relikd/cad-mouse-mk2-case-variations/spring/attempts/batch-1/v3.png

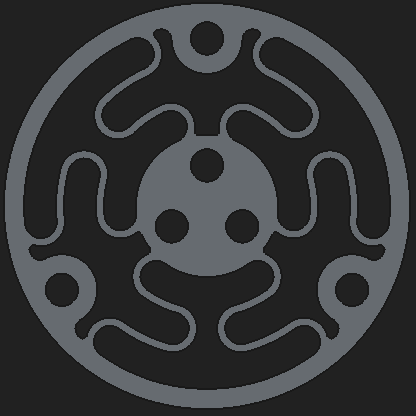
spring/attempts/batch-1/v3.png
