relikd/cad-mouse-mk2-case-variations/spring/attempts/batch-1/v17-winner.png

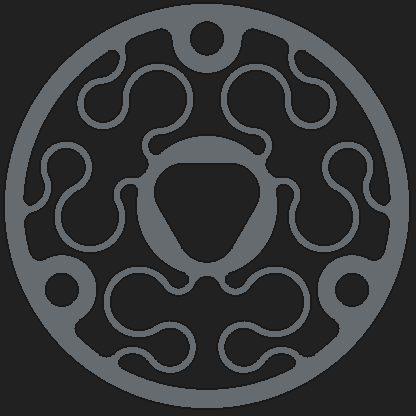
spring/attempts/batch-1/v17-winner.png
