relikd/cad-mouse-mk2-case-variations/_pcb/nikki-mcu.FCStd

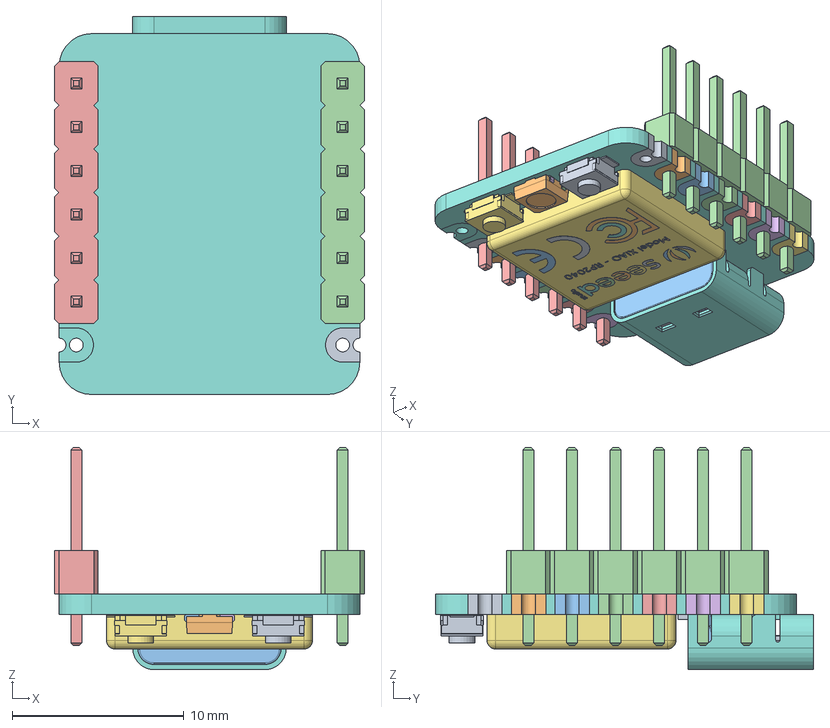
[picture p36: CAD file, 2026-06-23]
_pcb/nikki-mcu.FCStd
18.0 x 22.0 x 12.9 mm
type-c v2
type-c v001
type-c v002
type-c v003
type-c v004
type-c v005
type-c v006
type-c v007
type-c v008
type-c v009
type-c v010
type-c v011
type-c v012
type-c v013
type-c v014
type-c v015
type-c v016
type-c v017
type-c v018
type-c v019
type-c v020
type-c v021
type-c v022
type-c v023
smd_button v3
DOUT
DIN
VSS
VDD
smd_button v3(Mirror)
PinHeader_1x06_P2.54mm_Vertical
PinHeader_1x06_P2.54mm_Vertical001
