relikd/cad-mouse-mk2-case-variations/original/spring-spacer.FCStd

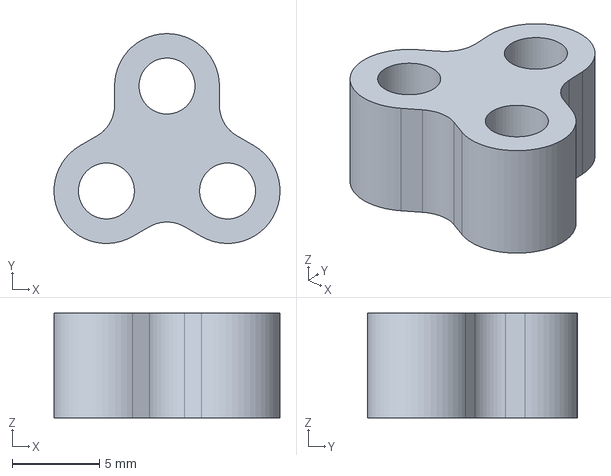
[picture p37: CAD file, 2026-06-12]
original/spring-spacer.FCStd
12.9 x 12.0 x 6.00 mm
