relikd/cad-mouse-mk2-case-variations/original/STEP/Base _Top.step

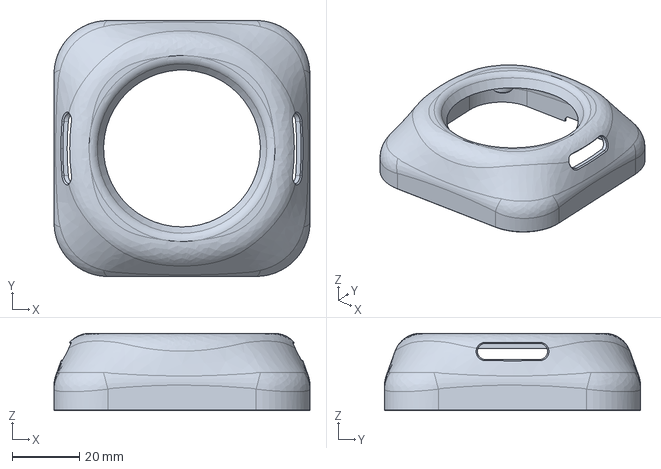
[picture p38: CAD file, 2026-07-06]
original/STEP/Base _Top.step
76.0 x 76.0 x 23.0 mm
