relikd/cad-mouse-mk2-case-variations/_pcb/original-sensorboard.FCStd

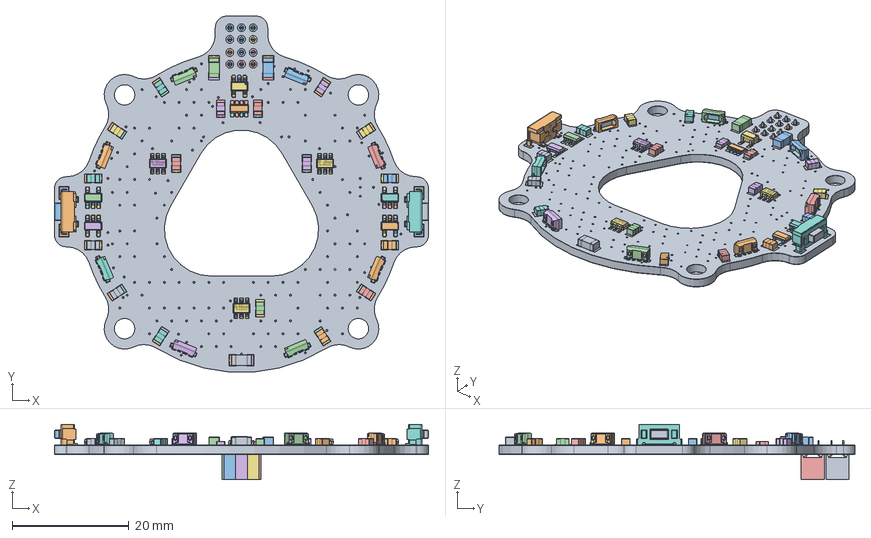
[picture p39: CAD file, 2026-06-12]
_pcb/original-sensorboard.FCStd
64.0 x 60.9 x 9.49 mm
Board
Board001
Board002
Board003
Board004
Board005
Board006
Board007
Board008
Board009
Board010
Board011
Board012
Board013
Board014
Board015
Board016
Board017
Board018
Board019
Board020
Board021
Board022
Board023
Board024
Board025
Board026
Board027
Board028
Board029
Board030
Board031
Board032
Board033
Board034
Board035
Board036
Board037
Board038
Board039
Board040
Board041
Board042
Board043
Board044
Board045
Board046
Board047
Board048
Board049
Board050
Board051
Board052
Board053
Board054
Board055
Board056
Board057
Board058
Board059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
