relikd/cad-mouse-mk2-case-variations/original/STEP/Base _Bottom Lid.step

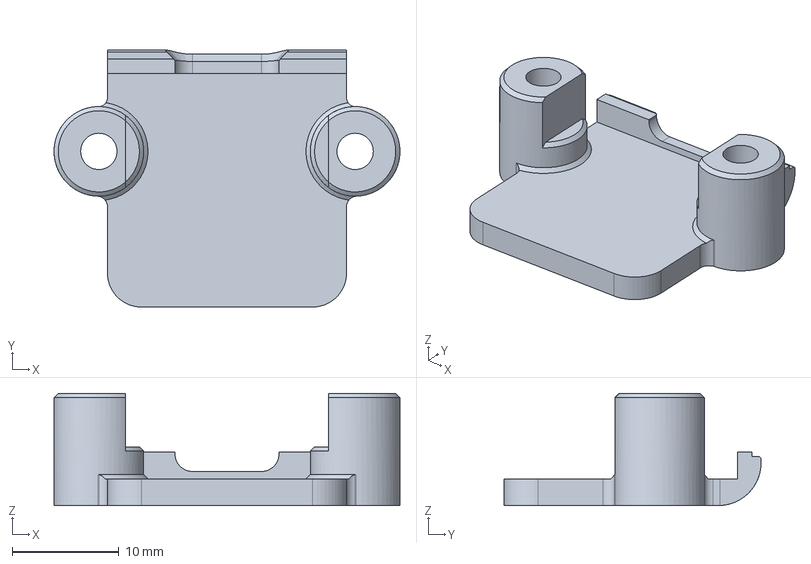
[picture p40: CAD file, 2026-07-06]
original/STEP/Base _Bottom Lid.step
32.4 x 24.1 x 10.5 mm
