relikd/cad-mouse-mk2-case-variations/spring/STL/SCS_CF_spacer.stl

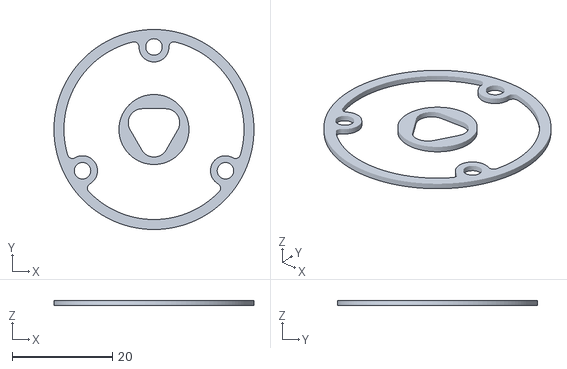
[picture p41: CAD file, 2026-07-11]
spring/STL/SCS_CF_spacer.stl
40.0 x 40.0 x 1.00
