relikd/cad-mouse-mk2-case-variations/_pcb/original-mcu.FCStd

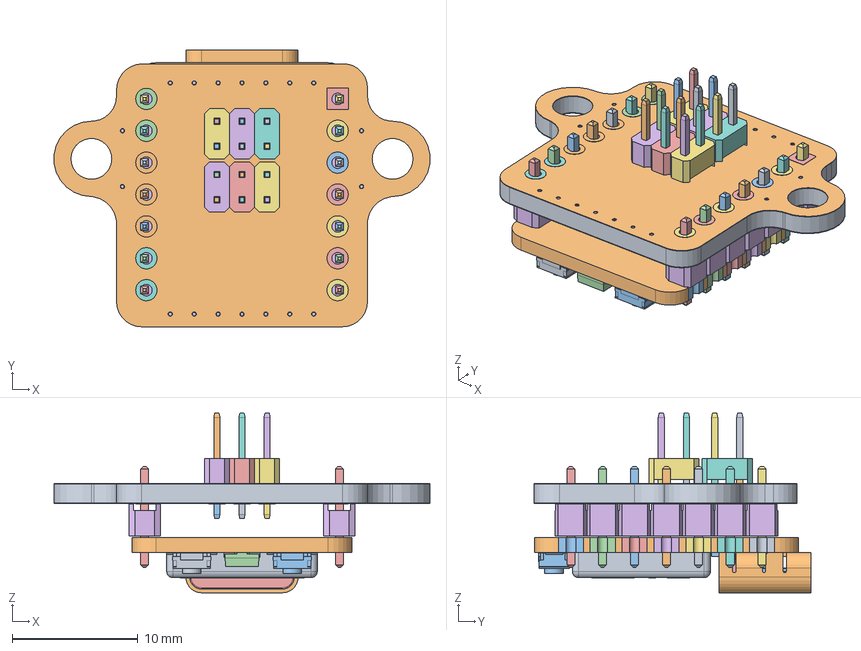
[picture p42: CAD file, 2026-06-12]
_pcb/original-mcu.FCStd
30.0 x 22.0 x 14.3 mm
Board201
Board202
Board203
Board204
Board205
Board206
Board207
Board208
Board209
Board210
Board211
Board212
Board213
Board214
Board215
Board216
Board217
Board218
Board219
Board220
Board221
Board222
Board223
Board224
Board225
Board226
Board227
Board228
Board229
Board230
Board231
Board232
Board233
Board234
Board235
Board236
Board237
Board238
Board239
Board240
Board241
Board242
Board243
Board244
Board245
1-copper094
1-copper095
1-copper096
1-copper097
1-copper098
1-copper099
1-copper100
1-copper101
1-copper102
1-copper103
1-copper104
1-copper105
1-copper106
1-copper107
1-copper108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
