relikd/cad-mouse-mk2-case-variations/original/stem.FCStd

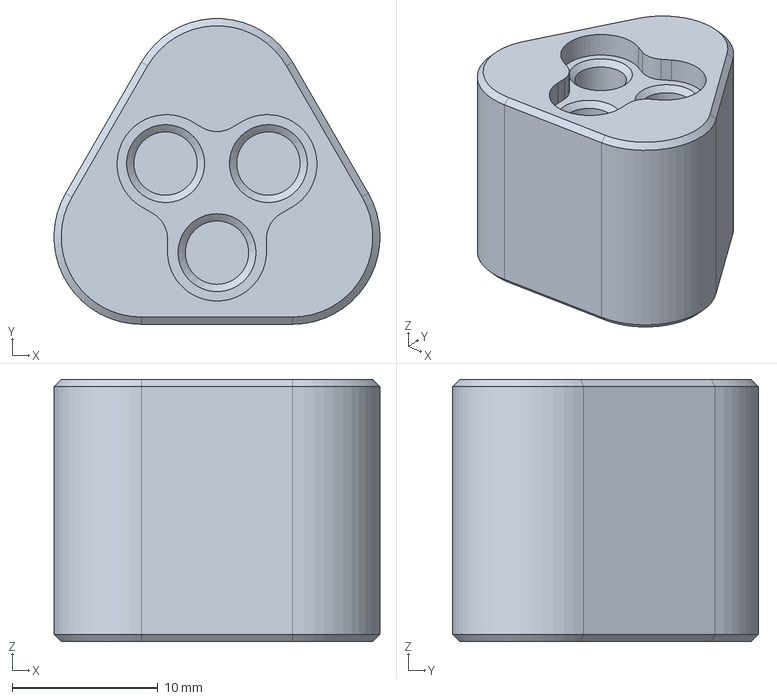
[picture p43: CAD file, 2026-06-12]
original/stem.FCStd
22.4 x 21.0 x 18.0 mm
