relikd/cad-mouse-mk2-case-variations/original/STEP/Diffuser.step

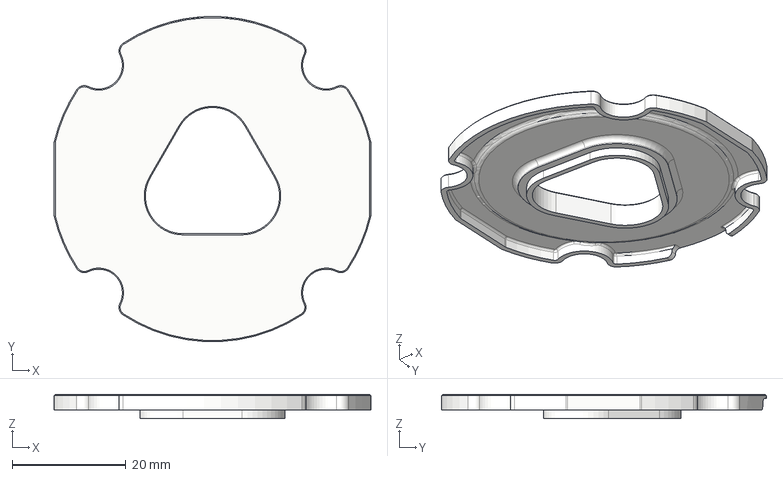
[picture p44: CAD file, 2026-07-06]
original/STEP/Diffuser.step
55.7 x 57.2 x 4.24 mm
